Heavy-Vehicle-Networking-At-U-Tulsa/CAN-Logger-3/tests/test_LEDs/test_LEDs.ino

//Setup LEDs
#define GREEN_LED 6
#define RED_LED 14
#define YELLOW_LED 5
#define BLUE_LED 39

boolean GREEN_LED_state;
boolean RED_LED_state;
boolean YELLOW_LED_state;
boolean BLUE_LED_state;

void setup() {
  // put your setup code here, to run once:
  // put your setup code here, to run once:
  pinMode(GREEN_LED, OUTPUT);
  pinMode(YELLOW_LED, OUTPUT);
  pinMode(RED_LED, OUTPUT);
  pinMode(BLUE_LED, OUTPUT);
  GREEN_LED_state = HIGH;
  YELLOW_LED_state = HIGH;
  RED_LED_state = HIGH;
  BLUE_LED_state = HIGH;
  digitalWrite(GREEN_LED,GREEN_LED_state);
  digitalWrite(YELLOW_LED,YELLOW_LED_state);
  digitalWrite(RED_LED,RED_LED_state);
  digitalWrite(BLUE_LED,BLUE_LED_state);
}

void loop() {
  // put your main code here, to run repeatedly:

}
